bitaxeorg/bitaxeNaja/3d/TPS546D24ARVFR.step

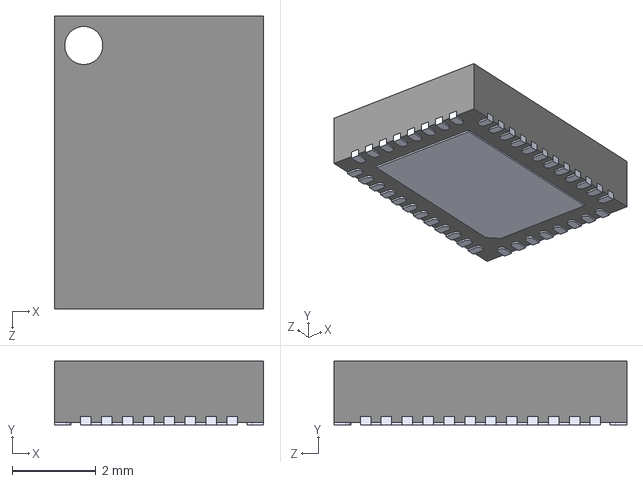
[picture p17: CAD file, 2025-07-17]
3d/TPS546D24ARVFR.step
5.00 x 1.52 x 7.00 mm
