bitaxeorg/bitaxeNaja/3d/BitaxeGT_heatsink.step

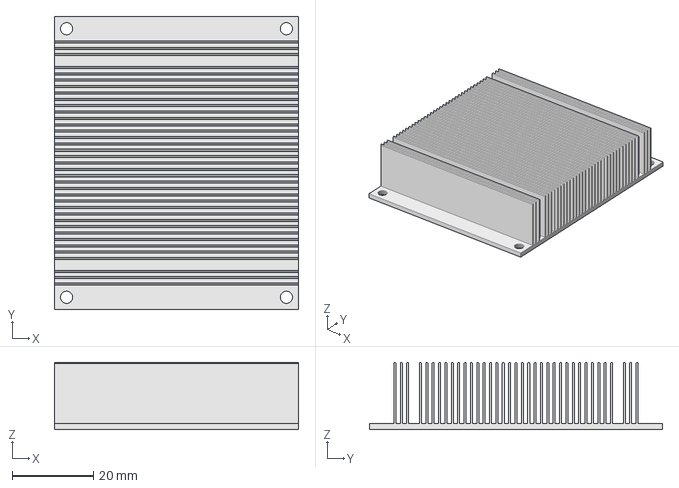
[picture p18: CAD file, 2025-07-17]
3d/BitaxeGT_heatsink.step
60.0 x 72.0 x 16.5 mm
