bitaxeorg/bitaxeNaja/3d/BM04B-SRSS-TB.STEP

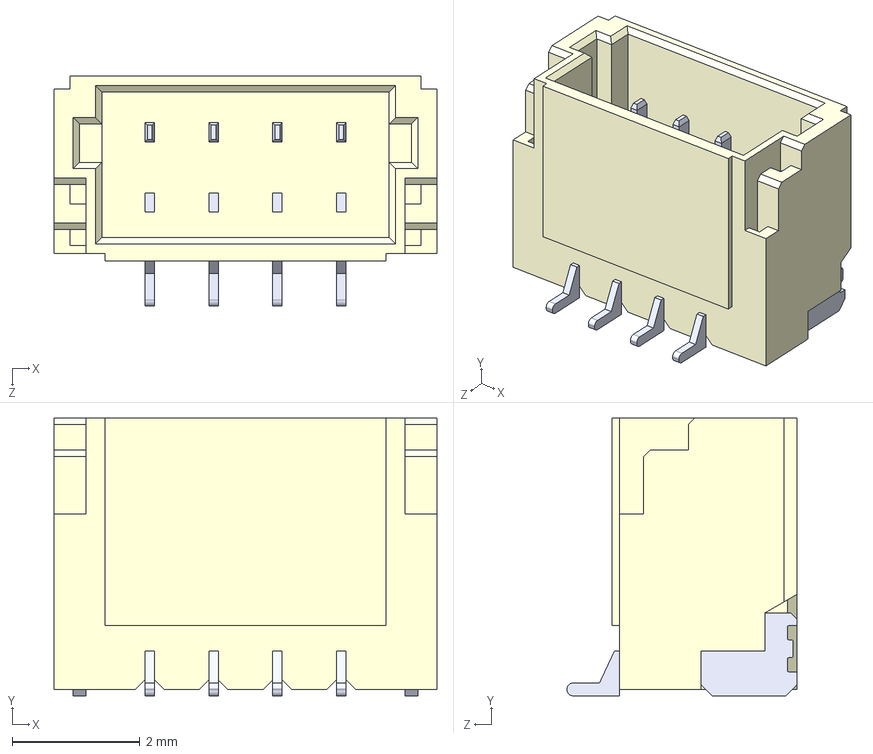
[picture p19: CAD file, 2025-07-17]
3d/BM04B-SRSS-TB.STEP
6.00 x 4.35 x 3.60 mm
