bitaxeorg/bitaxeNaja/3d/SLC1175-271MEC_COC.step

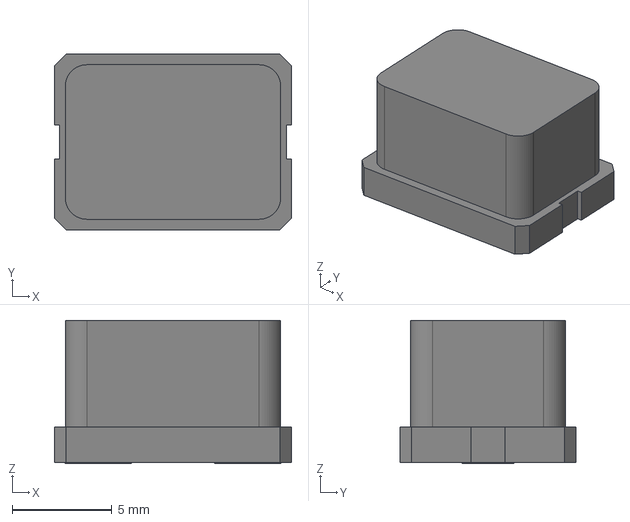
[picture p22: CAD file, 2025-07-17]
3d/SLC1175-271MEC_COC.step
11.9 x 8.83 x 7.19 mm
