bitaxeorg/bitaxeNaja/3d/IHLP2020CZ.step

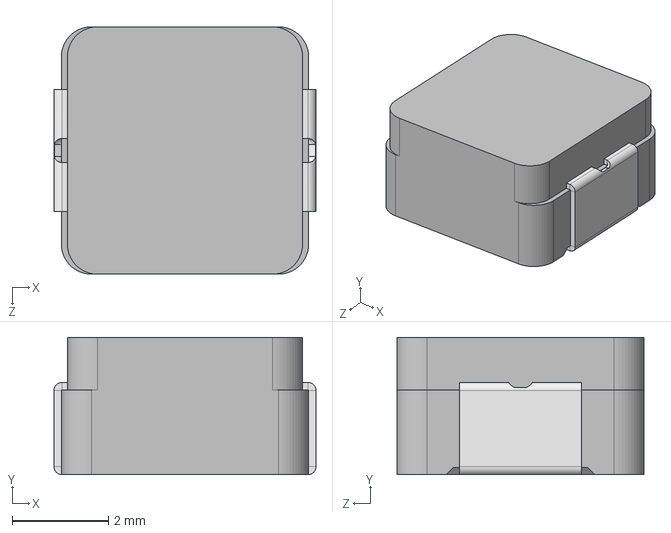
[picture p24: CAD file, 2025-07-17]
3d/IHLP2020CZ.step
5.45 x 2.86 x 5.15 mm
