bitaxeorg/bitaxeNaja/3d/TPSM863257RDXR--3DModel-STEP-510211.STEP

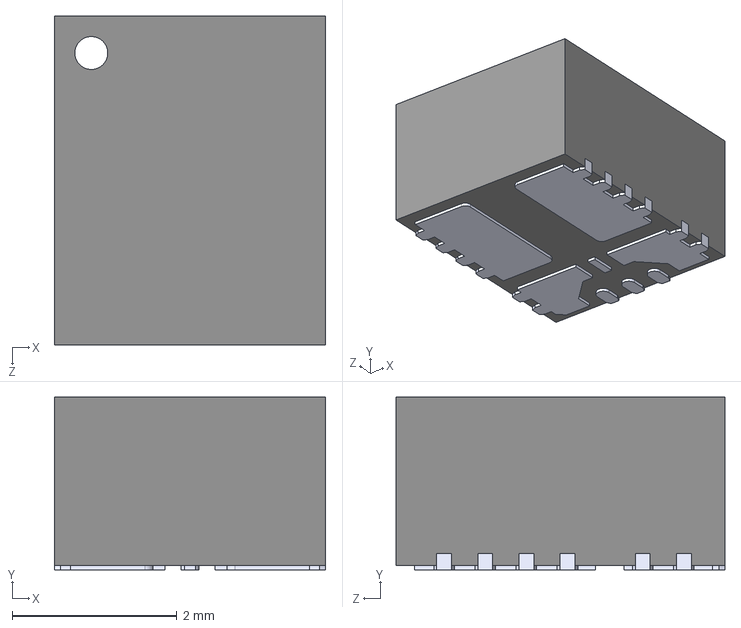
[picture p25: CAD file, 2025-07-17]
3d/TPSM863257RDXR--3DModel-STEP-510211.STEP
3.30 x 2.10 x 4.00 mm
