bitaxeorg/bitaxeNaja/3d/TSOT-23-5_RIT.step

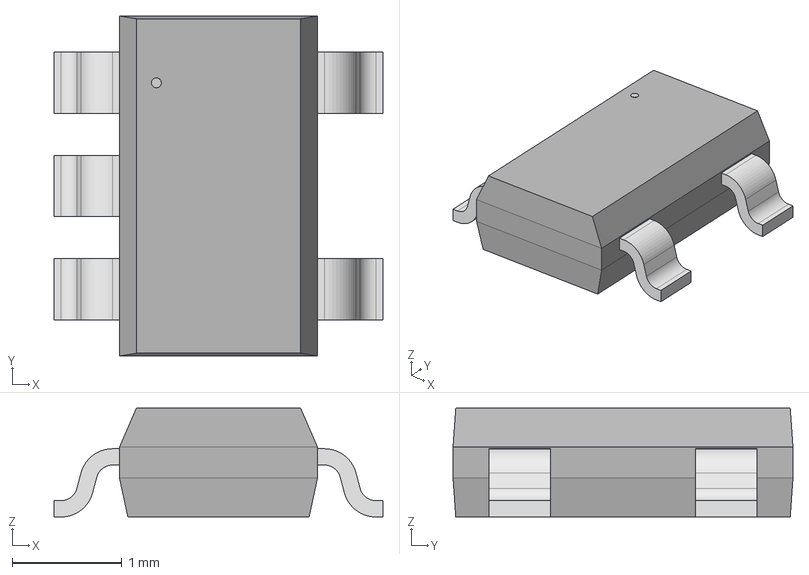
[picture p26: CAD file, 2025-07-17]
3d/TSOT-23-5_RIT.step
3.00 x 3.10 x 0.993 mm
