bitaxeorg/bitaxeNaja/3d/FFC2B35-08-T.STEP

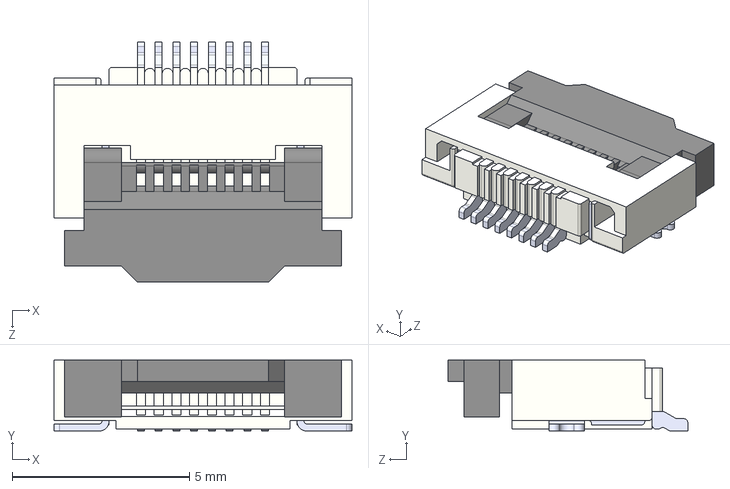
[picture p27: CAD file, 2025-07-17]
3d/FFC2B35-08-T.STEP
8.40 x 2.00 x 6.76 mm
