bitaxeorg/bitaxeNaja/3d/XTAL_SC32S-7PF20PPM_EPS.step

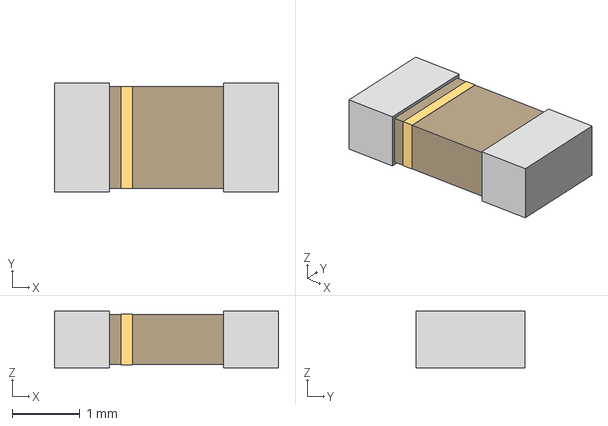
[picture p29: CAD file, 2025-07-17]
3d/XTAL_SC32S-7PF20PPM_EPS.step
3.30 x 1.60 x 0.838 mm
