bitaxeorg/bitaxeNaja/3d/BQB0016A.stp

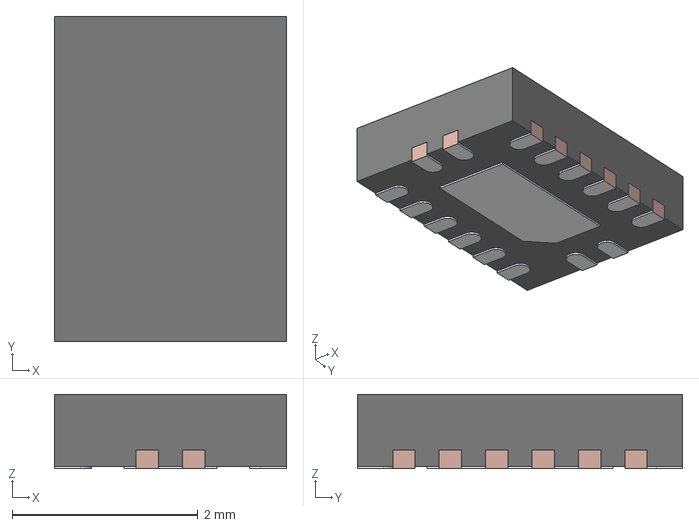
[picture p30: CAD file, 2025-07-17]
3d/BQB0016A.stp
2.50 x 3.50 x 0.8 mm
FRAME
