bitaxeorg/bitaxeNaja/3d/ST-4ETB2k_(202).stp

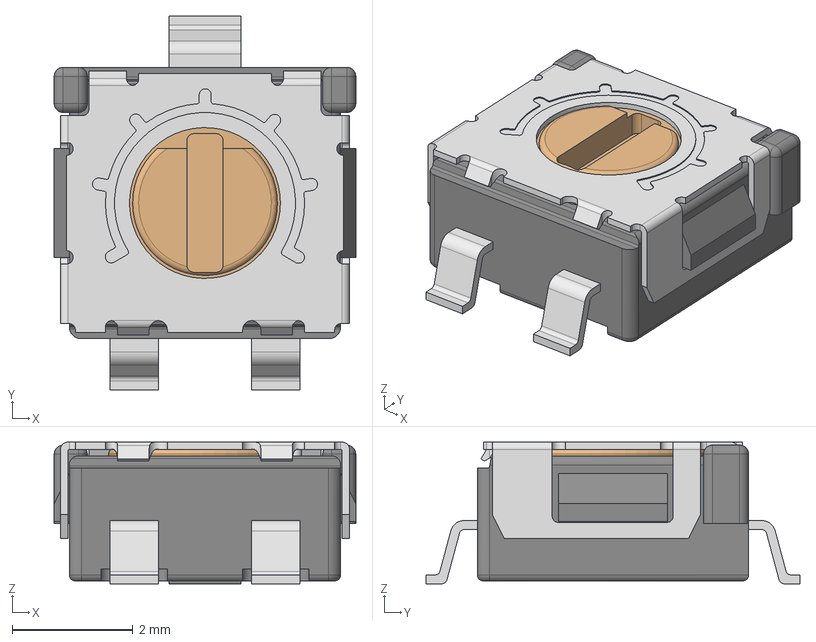
[picture p31: CAD file, 2025-07-17]
3d/ST-4ETB2k_(202).stp
5.00 x 6.20 x 2.35 mm
ST-4EB_terminal_2
ST-4EB_terminal
ST-4EB_terminal_1
ST-4-dial2
ST-4EB10X(100)_body
