bitaxeorg/bitaxeNaja/3d/SOT-23-5_M5_MCH.step

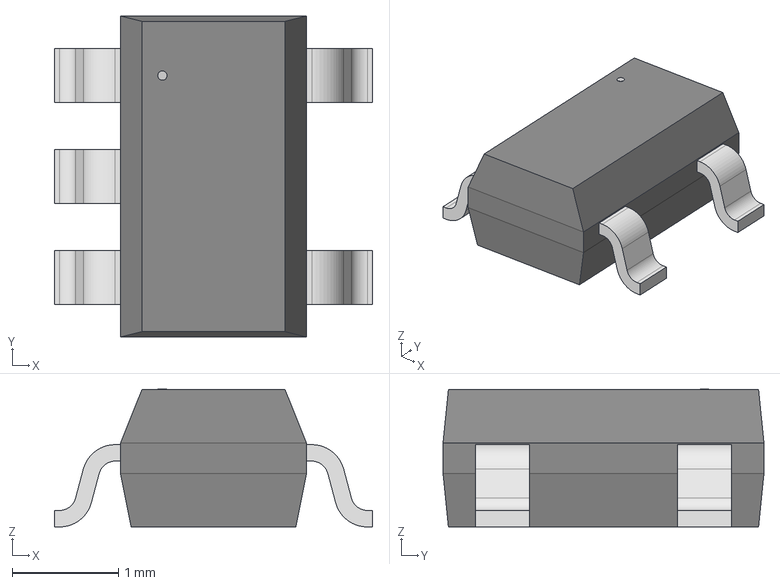
[picture p32: CAD file, 2025-07-17]
3d/SOT-23-5_M5_MCH.step
3.00 x 3.02 x 1.30 mm
