bitaxeorg/bitaxeNaja/3d/GT heatsink.step

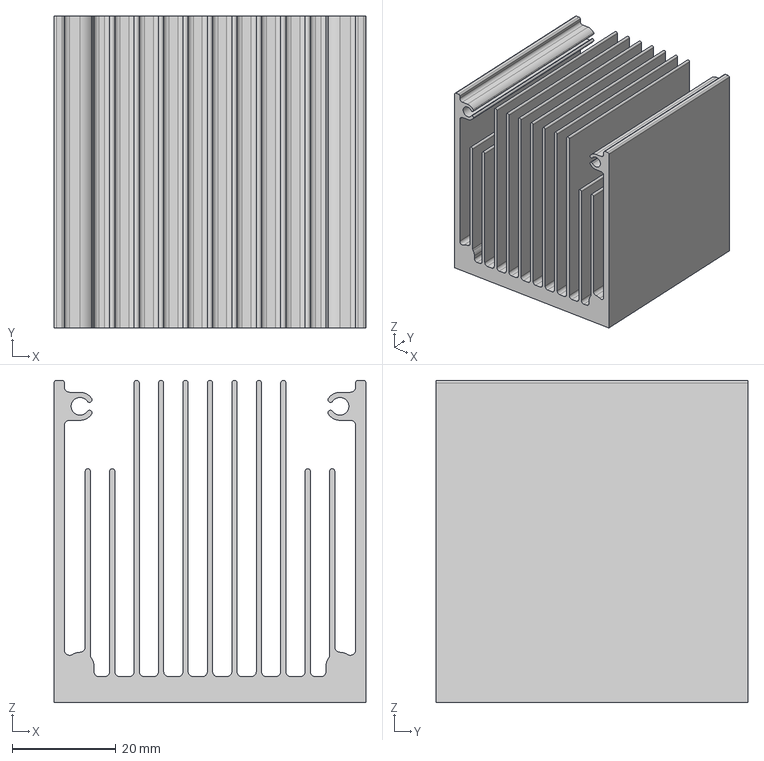
[picture p33: CAD file, 2025-07-17]
3d/GT heatsink.step
60.0 x 60.0 x 62.0 mm
