bitaxeorg/bitaxeNaja/3d/Bitaxe_Heatsink.step

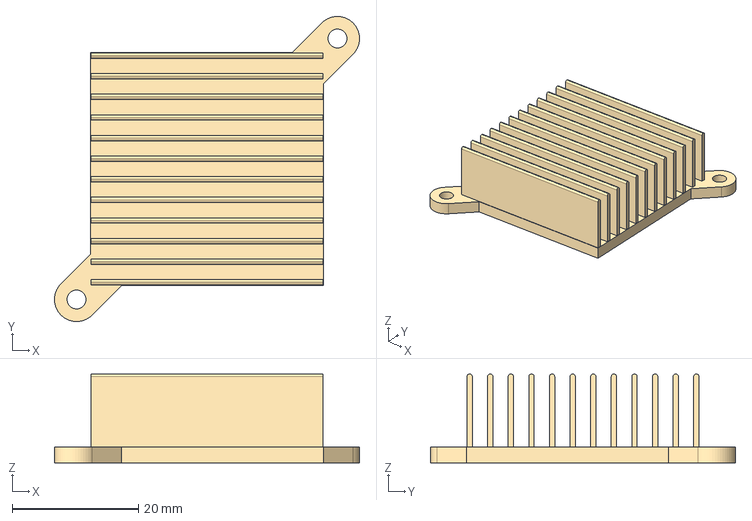
[picture p36: CAD file, 2025-07-17]
3d/Bitaxe_Heatsink.step
48.4 x 48.4 x 14.1 mm
