bitaxeorg/bitaxeNaja/3d/CS1213AG-tr.stp

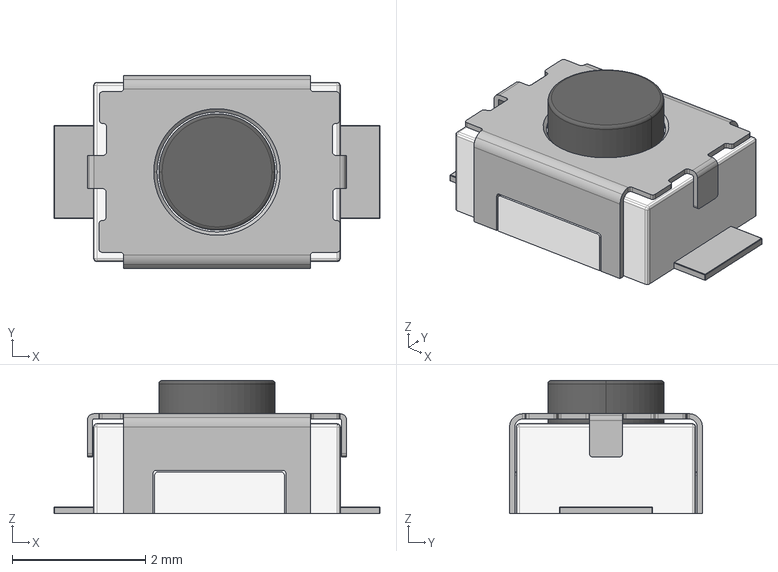
[picture p40: CAD file, 2025-07-17]
3d/CS1213AG-tr.stp
4.90 x 2.90 x 2.00 mm
