bitaxeorg/bitaxeNaja/3d/CX3225SB16000H0FLJCC.STEP

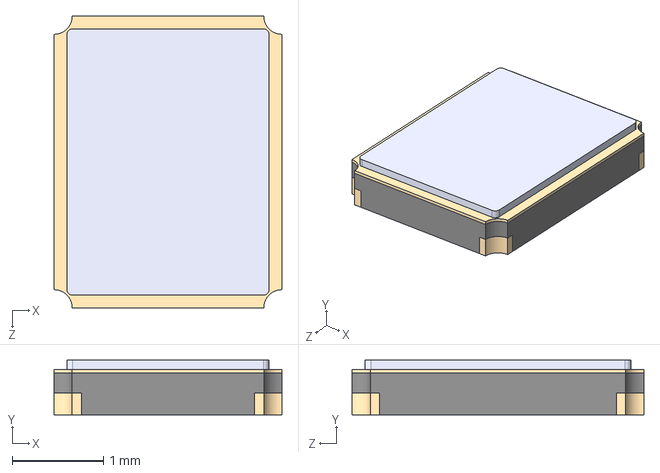
[picture p42: CAD file, 2025-07-17]
3d/CX3225SB16000H0FLJCC.STEP
2.50 x 0.6 x 3.20 mm
