bitaxeorg/bitaxeNaja/3d/SN74AXC1T45DBVR.STEP

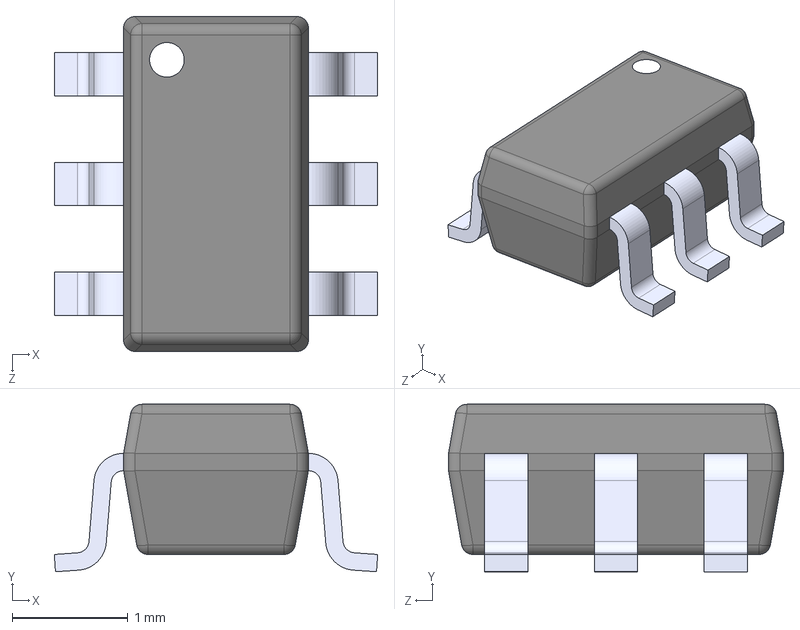
[picture p43: CAD file, 2025-07-17]
3d/SN74AXC1T45DBVR.STEP
2.80 x 1.45 x 2.90 mm
