bitaxeorg/bitaxeNaja/3d/141_TL3330AFxxxQG.stp

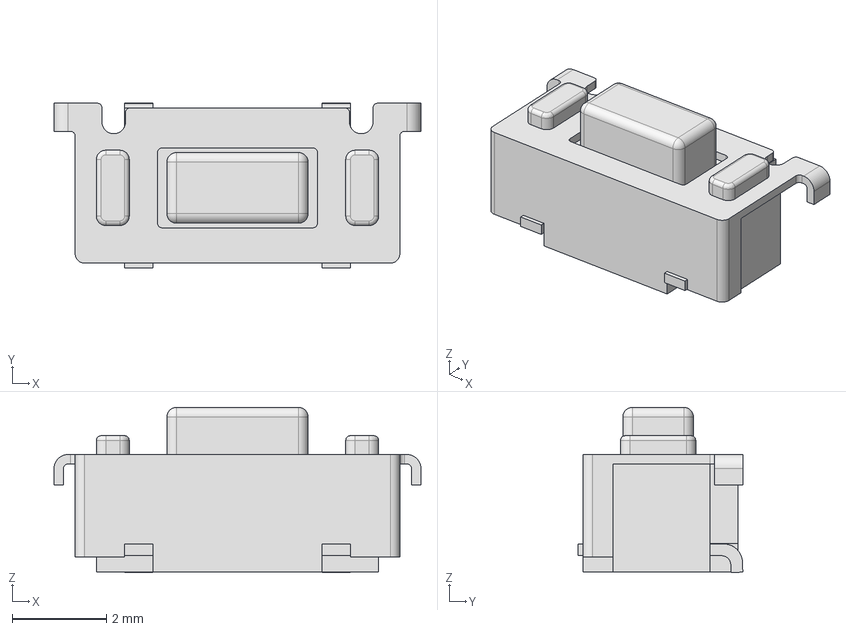
[picture p45: CAD file, 2025-07-17]
3d/141_TL3330AFxxxQG.stp
7.80 x 3.50 x 3.51 mm
