bitaxeorg/bitaxeNaja/3d/21-0164B_L622-1_MXM.step

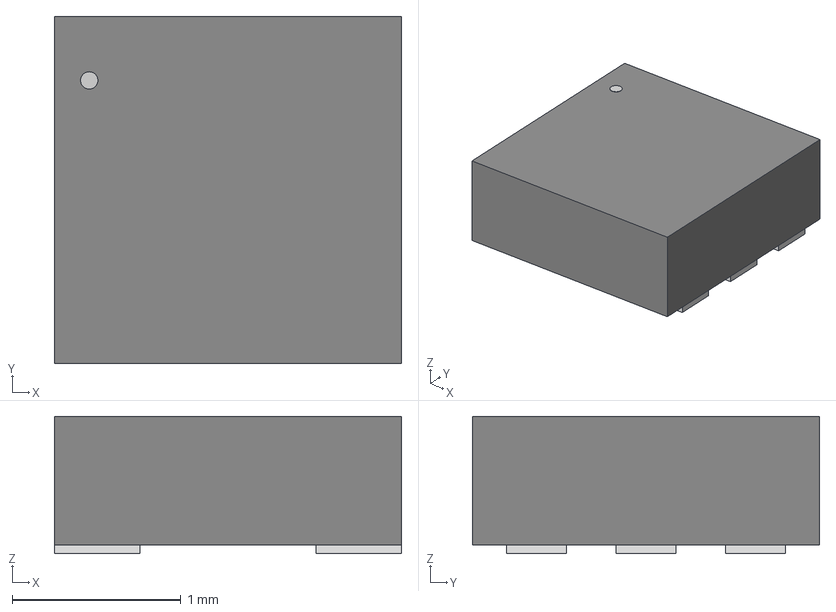
[picture p47: CAD file, 2025-07-17]
3d/21-0164B_L622-1_MXM.step
2.06 x 2.06 x 0.815 mm
