bitaxeorg/bitaxeNaja/3d/CUI_DEVICES_PJ-002AH.step

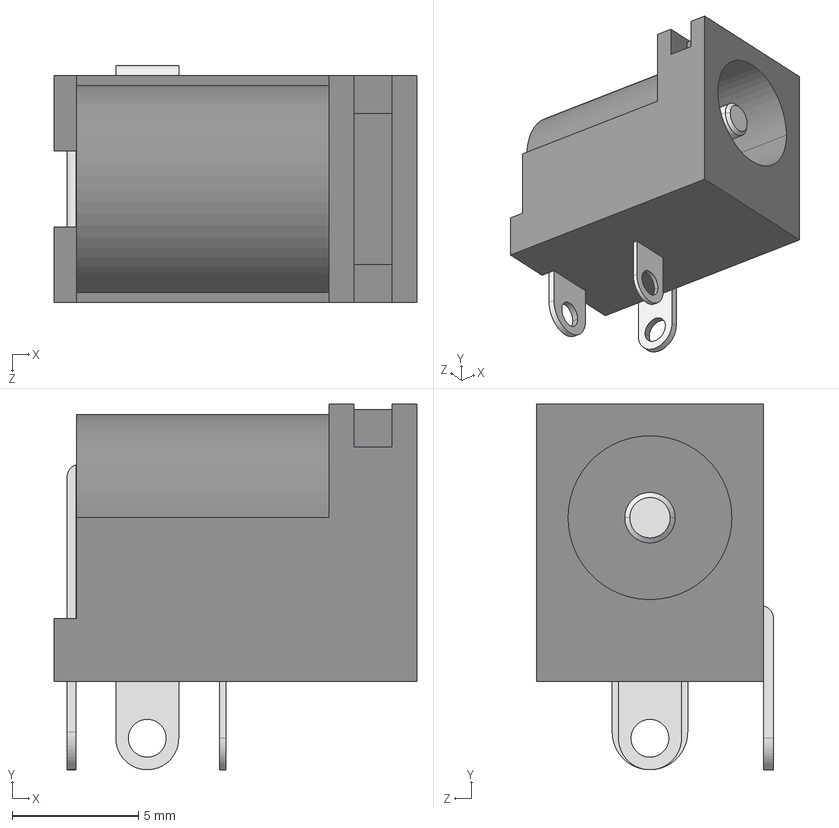
[picture p49: CAD file, 2025-07-17]
3d/CUI_DEVICES_PJ-002AH.step
14.4 x 14.5 x 9.40 mm
