bitaxeorg/bitaxeNaja/3d/CUI_DEVICES_PJ-037AH.step

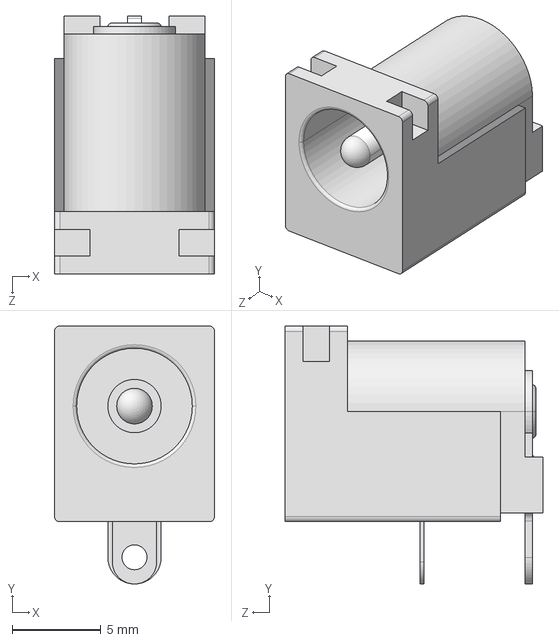
[picture p50: CAD file, 2025-07-17]
3d/CUI_DEVICES_PJ-037AH.step
9.00 x 14.5 x 14.5 mm
