bitaxeorg/bitaxeNaja/3d/SMV_z90.stp

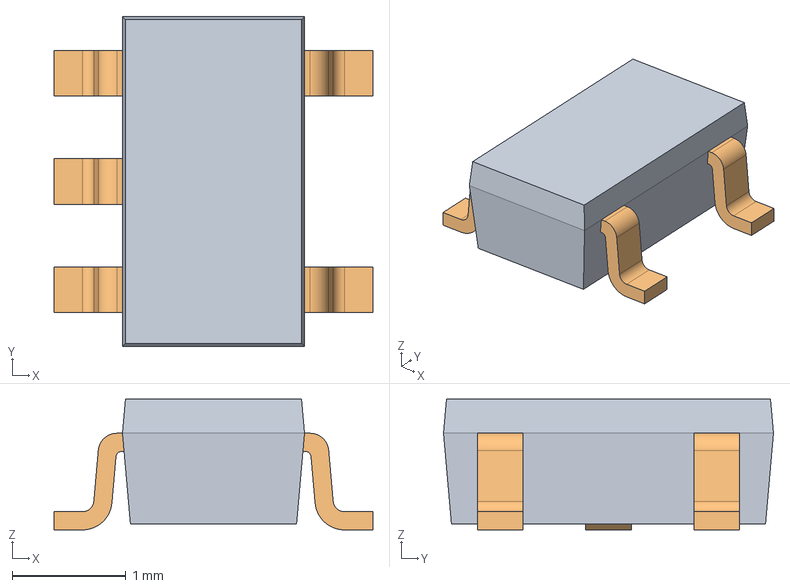
[picture p52: CAD file, 2025-07-17]
3d/SMV_z90.stp
2.80 x 2.90 x 1.15 mm
