bitaxeorg/bitaxeNaja/3d/IND_-1R5MC_SUM.step

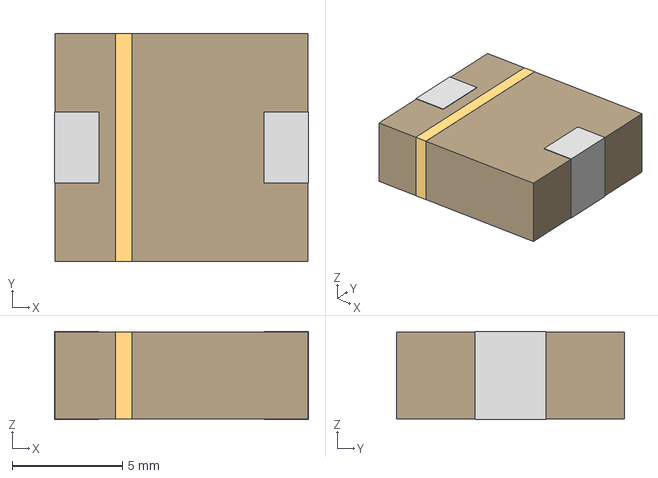
[picture p55: CAD file, 2025-07-17]
3d/IND_-1R5MC_SUM.step
11.5 x 10.3 x 3.99 mm
