bitaxeorg/bitaxeNaja/3d/XT30PW-M.stp

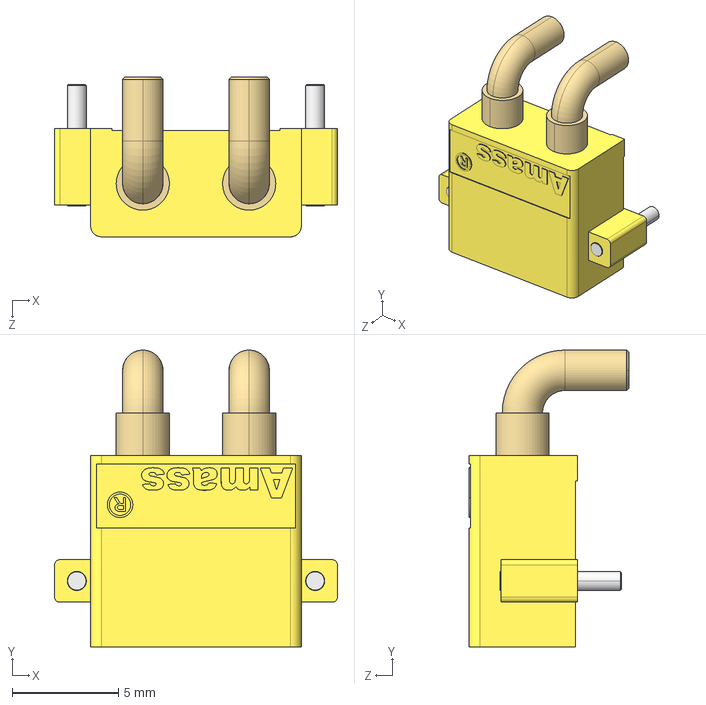
[picture p56: CAD file, 2025-07-17]
3d/XT30PW-M.stp
13.3 x 13.9 x 7.50 mm
