bitaxeorg/bitaxeNaja/3d/bm1370.step

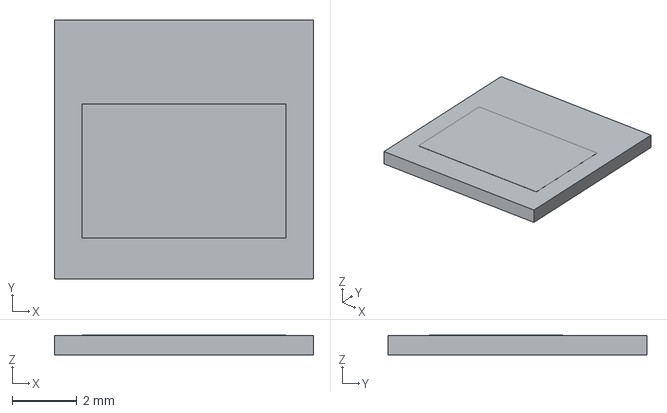
[picture p58: CAD file, 2025-07-17]
3d/bm1370.step
8.00 x 8.00 x 0.61 mm
