bitaxeorg/bitaxeNaja/3d/QFN16_4X4_MCH.step

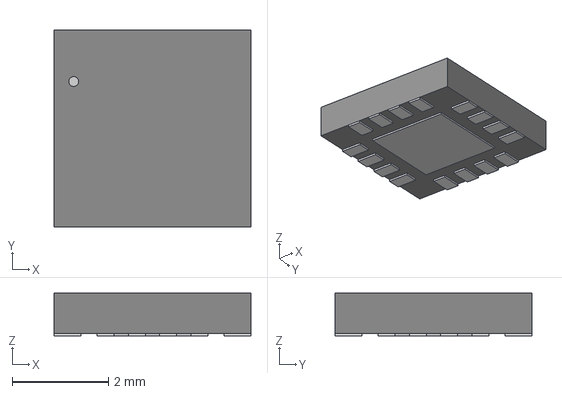
[picture p60: CAD file, 2025-07-17]
3d/QFN16_4X4_MCH.step
4.09 x 4.09 x 0.892 mm
