bitaxeorg/bitaxeNaja/3d/Coilcraft-SLC1175.STEP

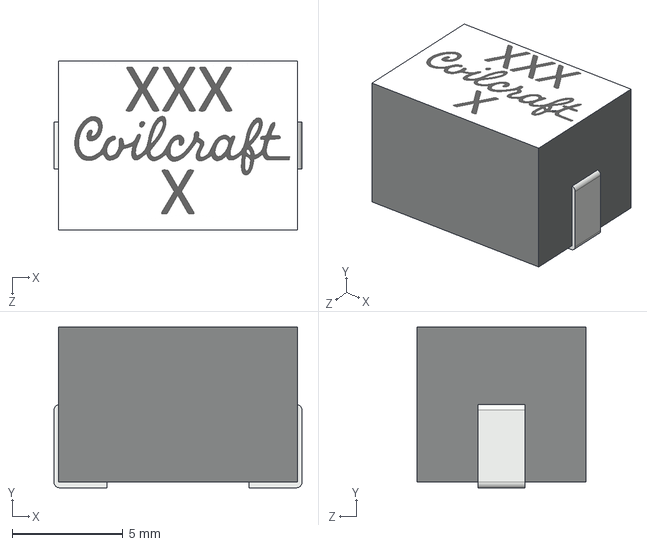
[picture p63: CAD file, 2025-07-17]
3d/Coilcraft-SLC1175.STEP
11.2 x 7.25 x 7.65 mm
